kajusK/GLogger/fw/app/src/storage.c

/*
 * Copyright (C) 2019 Jakub Kaderka
 *
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
 * You should have received a copy of the GNU General Public License
 * along with this program.  If not, see <https://www.gnu.org/licenses/>.
 */

/**
 * @file    app/storage.c
 * @brief   Storing GPS data into external flash
 *
 * @addtogroup app
 * @{
 */

#include <string.h>

#include "drivers/spi_flash.h"
#include "desc.h"
#include "config.h"
#include "storage.h"

static uint32_t storagei_offset = 0;

/**
 * Check if storage item is empty (all bits are 0xff - erased flash)
 *
 * @param item      Item to be checked
 * @return true if empty
 */
static bool Storagei_ItemEmpty(const storage_item_t *item)
{
    const uint8_t *pos = (uint8_t *) item;

    for (size_t i = 0; i < sizeof(storage_item_t); i++) {
        if (*pos++ != 0xff) {
            return false;
        }
    }
    return true;
}

/**
 * Check if item on selected offset is end of log mark
 *
 * @param item  Item to be checked
 * @return true if EOL
 */
bool Storage_IsEOL(const storage_item_t *item)
{
    const uint8_t *pos = (uint8_t *) item;

    for (size_t i = 0; i < sizeof(storage_item_t); i++) {
        if (*pos++ != 0x00) {
            return false;
        }
    }
    return true;
}

void Storage_Erase(void)
{
    SpiFlash_Erase(&spiflash_desc);
    storagei_offset = 0;
}

size_t Storage_SpaceRemaining(void)
{
    return (STORAGE_SIZE - storagei_offset)/sizeof(storage_item_t);
}

size_t Storage_SpaceUsed(void)
{
    return storagei_offset/sizeof(storage_item_t);
}

size_t Storage_GetSize(void)
{
    return STORAGE_SIZE/sizeof(storage_item_t);
}

bool Storage_Add(const gps_info_t *info)
{
    storage_item_t item;

    if (Storage_SpaceRemaining() == 0) {
        return false;
    }

    item.lat = info->lat.num;
    item.lat_scale = info->lat.scale;
    item.lon = info->lon.num;
    item.lon_scale = info->lon.scale;
    item.timestamp = info->timestamp;
    item.elevation_m = info->altitude_dm / 10;

    SpiFlash_Write(&spiflash_desc, storagei_offset, (uint8_t *) &item,
            sizeof(item));
    storagei_offset += sizeof(item);
    return true;
}

bool Storage_Get(uint32_t id, storage_item_t *item)
{
    uint32_t offset = id * sizeof(storage_item_t);
    if (offset >= storagei_offset) {
        return false;
    }

    SpiFlash_Read(&spiflash_desc, offset, (uint8_t *) item,
            sizeof(storage_item_t));
    return true;
}

void Storage_Init(void)
{
    uint8_t buf[sizeof(storage_item_t)];
    uint8_t item_size = sizeof(storage_item_t);
    storagei_offset = 0;

    while (storagei_offset < STORAGE_SIZE) {
        SpiFlash_Read(&spiflash_desc, storagei_offset, buf, item_size);
        if (Storagei_ItemEmpty((storage_item_t *) buf)) {
            break;
        }
        storagei_offset += item_size;
    }
    /* Add new invalid item - end of log record */
    if (storagei_offset != 0) {
        SpiFlash_Read(&spiflash_desc, storagei_offset - item_size, buf,
                item_size);
        if (!Storage_IsEOL((storage_item_t *) buf)) {
            memset(buf, 0x00, item_size);
            SpiFlash_Write(&spiflash_desc, storagei_offset, buf, item_size);
            storagei_offset += item_size;
        }
    }
}

/** @} */
